regnaDkciN/Filament-Scale/SourceFiles/JmcFilamentScale/ScaleIcon.cpp

/////////////////////////////////////////////////////////////////////////////////
// ScaleIcon.cpp
//
// Contains the array that has  the bit pattern for the welcome screen scale
// icon.
//
// History:
// - jmcorbett 14-JUN-2021 Original creation.
//
// Copyright (c) 2021, Joseph M. Corbett
/////////////////////////////////////////////////////////////////////////////////
#include "ScaleIcon.h"

const unsigned char ScaleIcon[] = {
	// 'Scale3, 120x120px
	0x00, 0x00, 0x00, 0x00, 0x00, 0x00, 0x00, 0x00, 0x00, 0x00, 0x00, 0x00, 0x00, 0x00, 0x00, 0x00,
	0x00, 0x00, 0x00, 0x00, 0x00, 0x00, 0x00, 0x00, 0x00, 0x00, 0x00, 0x00, 0x00, 0x00, 0x00, 0x00,
	0x00, 0x00, 0x00, 0x00, 0x00, 0x00, 0x00, 0x00, 0x00, 0x00, 0x00, 0x00, 0x00, 0x00, 0x00, 0x00,
	0x00, 0x00, 0x00, 0x00, 0x00, 0x00, 0x00, 0x00, 0x00, 0x00, 0x00, 0x00, 0x00, 0x00, 0x00, 0x00,
	0x00, 0x00, 0x00, 0x00, 0x00, 0x00, 0x00, 0x00, 0x00, 0x00, 0x00, 0x00, 0x00, 0x00, 0x00, 0x00,
	0x00, 0x00, 0x18, 0x00, 0x00, 0x00, 0x00, 0x00, 0x00, 0x00, 0x00, 0x00, 0x00, 0x00, 0x00, 0x00,
	0x00, 0x7e, 0x00, 0x00, 0x00, 0x00, 0x00, 0x00, 0x00, 0x00, 0x00, 0x00, 0x00, 0x00, 0x00, 0x00,
	0x7e, 0x00, 0x00, 0x00, 0x00, 0x00, 0x00, 0x00, 0x00, 0x00, 0x00, 0x00, 0x00, 0x00, 0x00, 0xff,
	0x00, 0x00, 0x00, 0x00, 0x00, 0x00, 0x00, 0x00, 0x00, 0x00, 0x00, 0x00, 0x00, 0x00, 0xff, 0x00,
	0x00, 0x00, 0x00, 0x00, 0x00, 0x00, 0x00, 0x00, 0x00, 0x00, 0x00, 0x00, 0x00, 0xff, 0x00, 0x00,
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
	0xff, 0xe0, 0x00, 0x00, 0x1f, 0xff, 0xc0, 0x00, 0x00, 0x03, 0xff, 0xf8, 0x00, 0x00, 0x07, 0xff,
	0xe0, 0x00, 0x00, 0x1f, 0xff, 0xc0, 0x00, 0x00, 0x03, 0xff, 0xfc, 0x00, 0x00, 0x03, 0xff, 0xc0,
	0x00, 0x00, 0x1f, 0xff, 0xc0, 0x00, 0x00, 0x07, 0xff, 0x7c, 0x00, 0x00, 0x01, 0xff, 0x80, 0x00,
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
};
